ManoloMancelli/Persephone-Pro-Controller/Docs/V1/IMG/Arduino Uno Mini.png

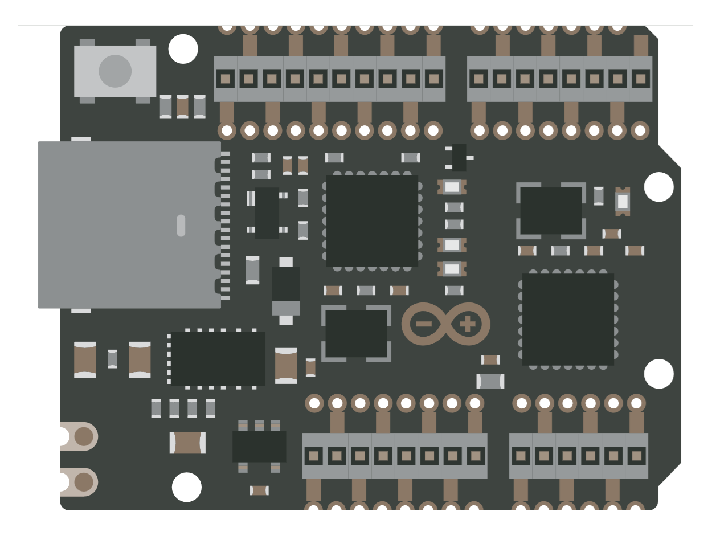
Docs/V1/IMG/Arduino Uno Mini.png
