ManoloMancelli/Persephone-Pro-Controller/img/V2/2.jpeg

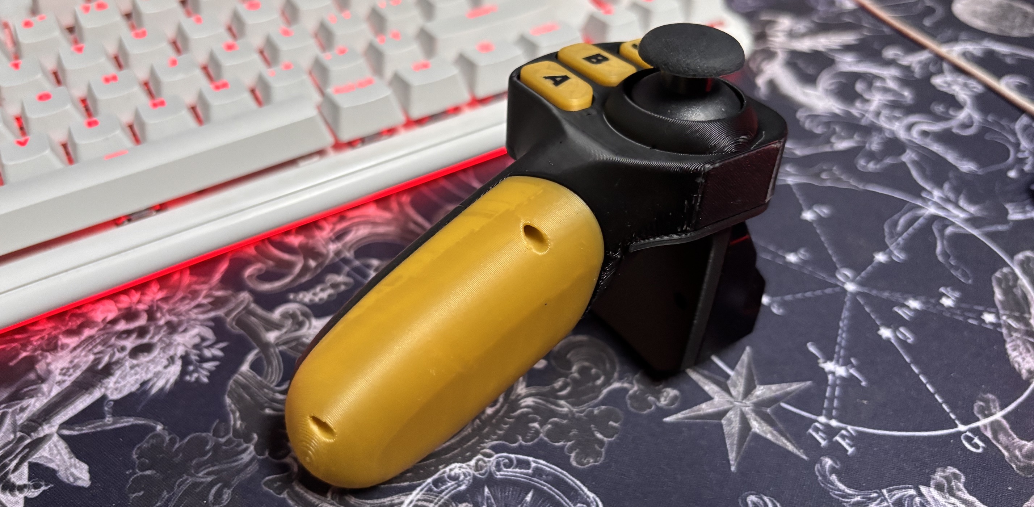
img/V2/2.jpeg
