ManoloMancelli/Persephone-Pro-Controller/img/V2/3.jpeg

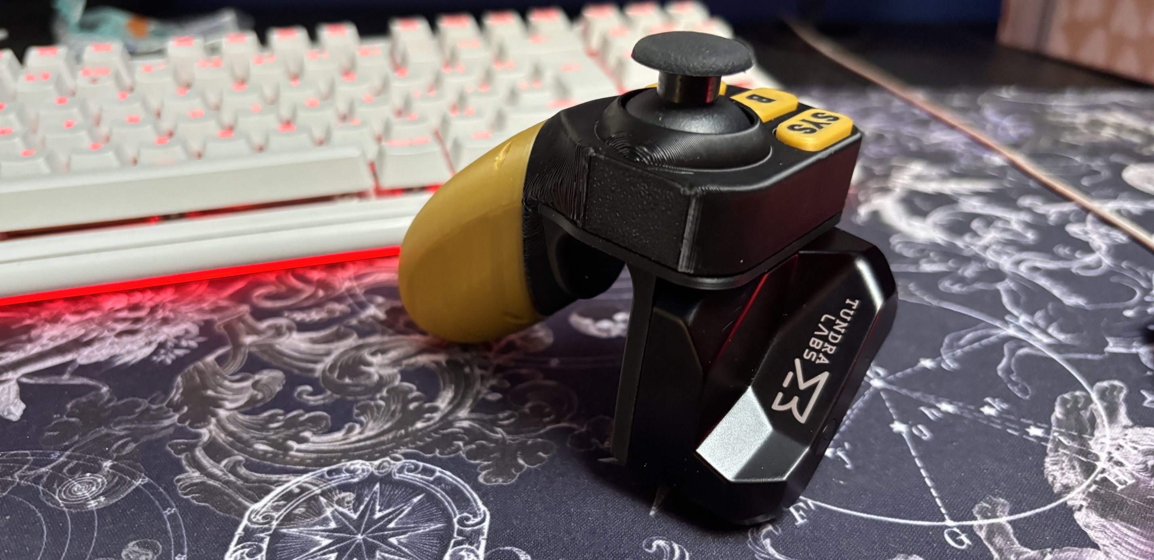
img/V2/3.jpeg
