ManoloMancelli/Persephone-Pro-Controller/Changelog/V1/img/11.01.2026/assembly3.jpeg

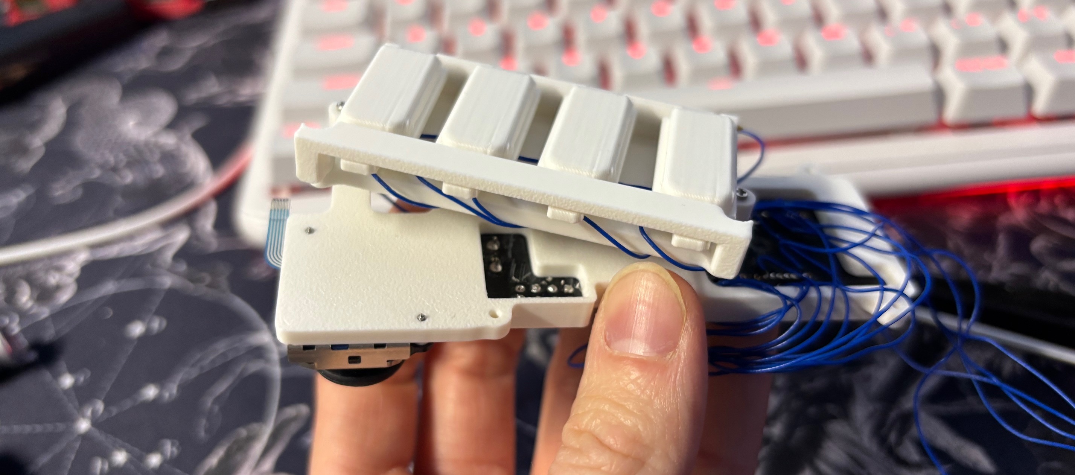
Changelog/V1/img/11.01.2026/assembly3.jpeg
