ManoloMancelli/Persephone-Pro-Controller/Changelog/V1/img/8.01.2026/array1.jpeg

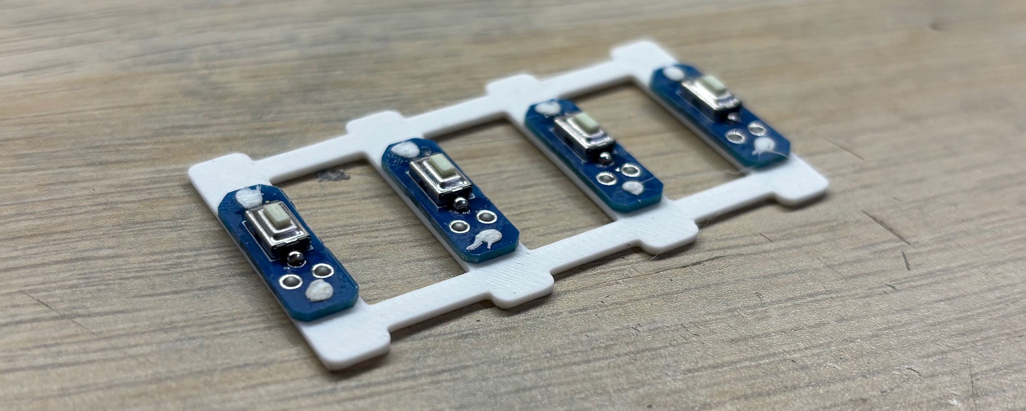
Changelog/V1/img/8.01.2026/array1.jpeg
