ManoloMancelli/Persephone-Pro-Controller/Changelog/V1/img/8.01.2026/joystick2.jpeg

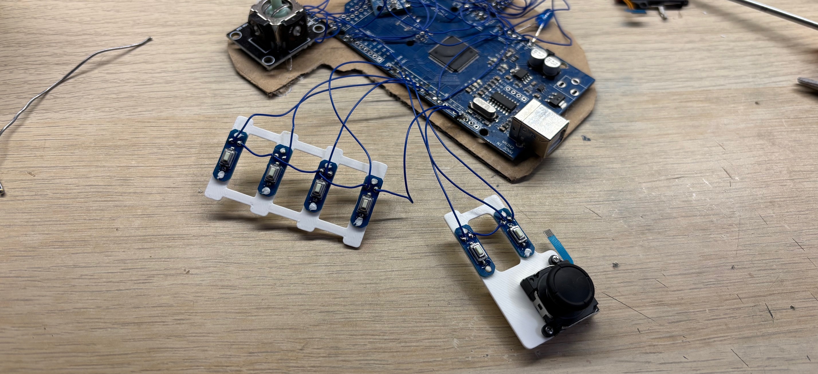
Changelog/V1/img/8.01.2026/joystick2.jpeg
