ManoloMancelli/Persephone-Pro-Controller/Changelog/V1/img/8.01.2026/prototype1.jpeg

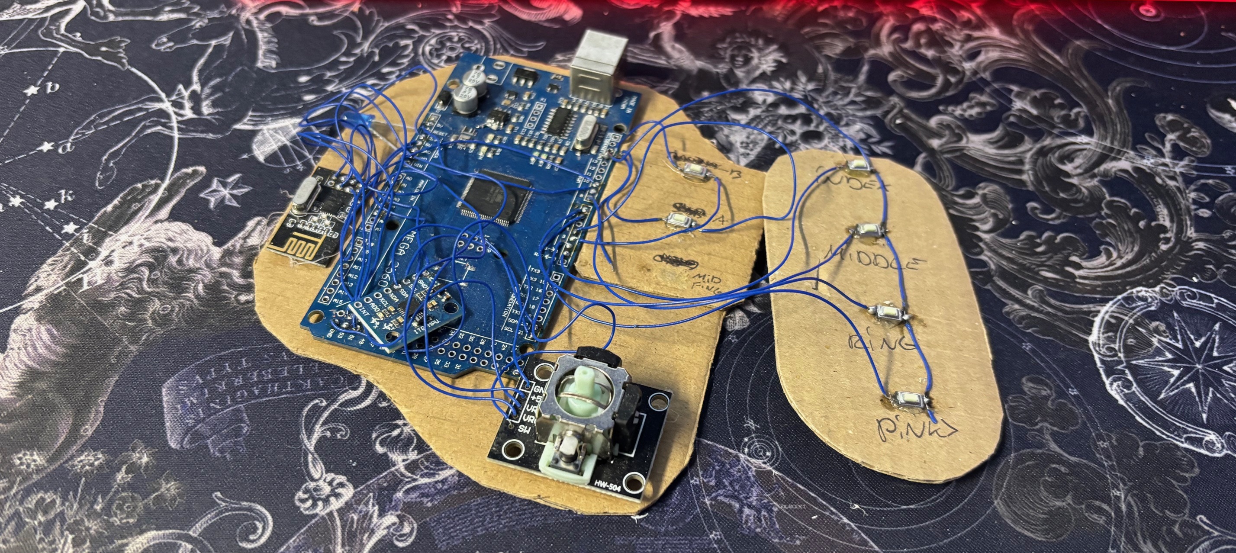
Changelog/V1/img/8.01.2026/prototype1.jpeg
