ManoloMancelli/Persephone-Pro-Controller/Changelog/V1/img/9.01.2026/connection1.jpeg

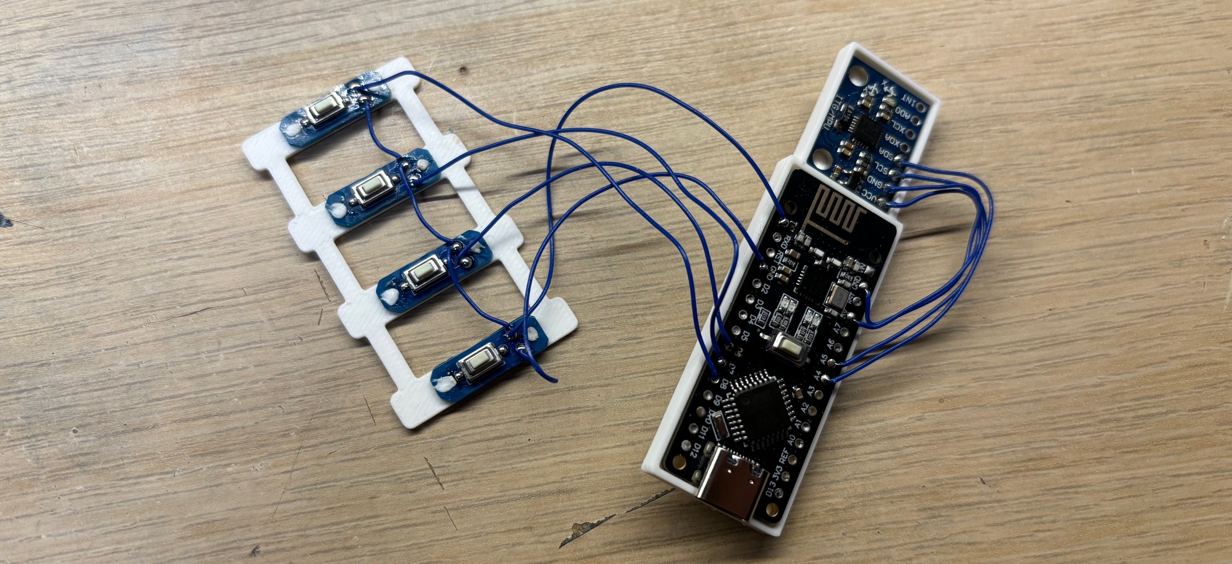
Changelog/V1/img/9.01.2026/connection1.jpeg
