ManoloMancelli/Persephone-Pro-Controller/Changelog/V1/img/9.01.2026/connection2.jpeg

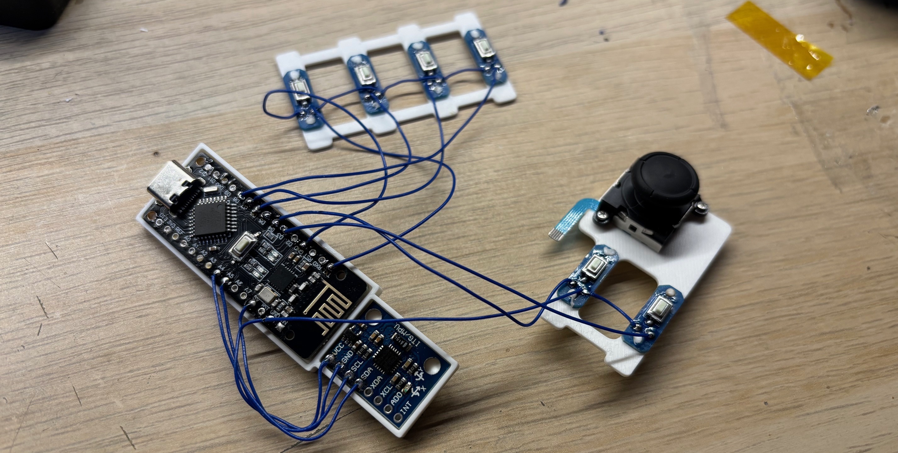
Changelog/V1/img/9.01.2026/connection2.jpeg
