ManoloMancelli/Persephone-Pro-Controller/Changelog/V1/img/10.01.2026/arduino1.png

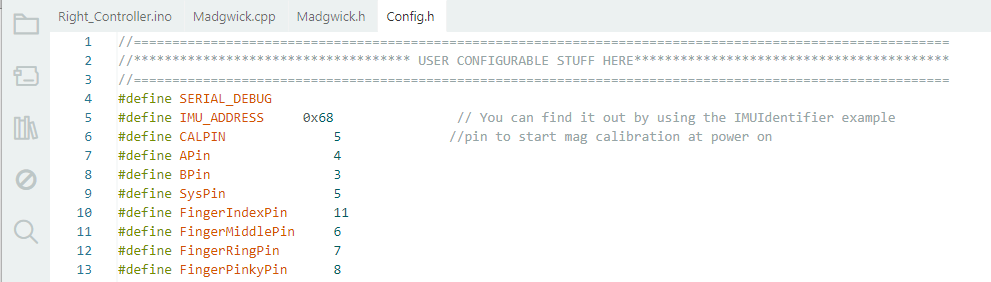
Changelog/V1/img/10.01.2026/arduino1.png
