ManoloMancelli/Persephone-Pro-Controller/Changelog/V1/img/10.01.2026/bracket2.jpeg

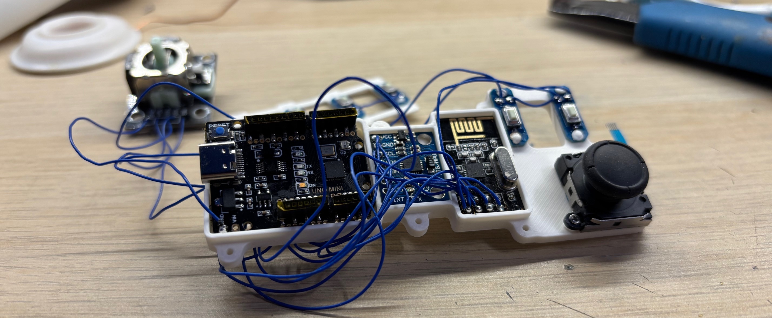
Changelog/V1/img/10.01.2026/bracket2.jpeg
