ManoloMancelli/Persephone-Pro-Controller/Changelog/V1/img/17.01.2026/joycon1.jpeg

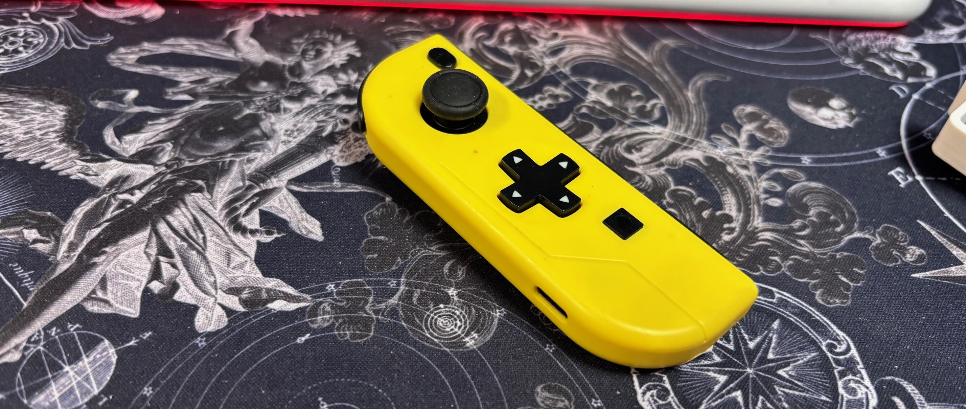
Changelog/V1/img/17.01.2026/joycon1.jpeg
