ManoloMancelli/Persephone-Pro-Controller/Changelog/V1/img/17.01.2026/joycon2.jpeg

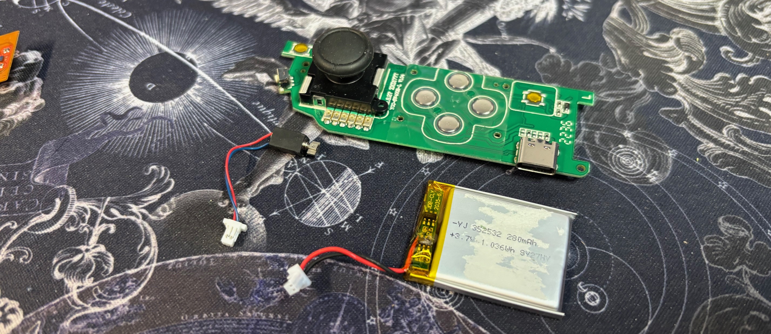
Changelog/V1/img/17.01.2026/joycon2.jpeg
