ManoloMancelli/Persephone-Pro-Controller/Changelog/V1/img/18.01.2026/bumper1.jpeg

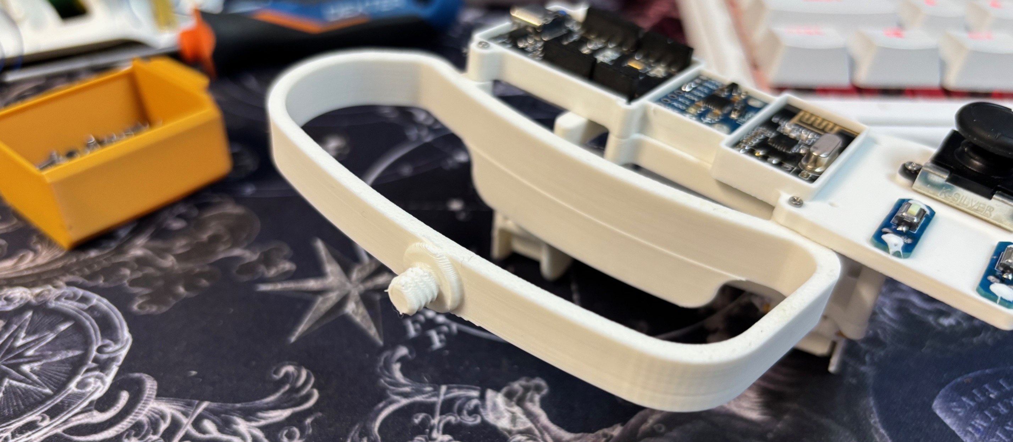
Changelog/V1/img/18.01.2026/bumper1.jpeg
