ManoloMancelli/Persephone-Pro-Controller/Changelog/V1/img/18.01.2026/palmrest.jpeg

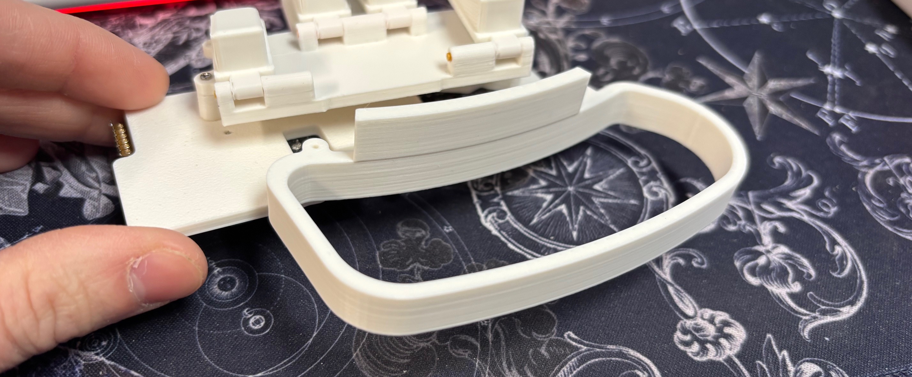
Changelog/V1/img/18.01.2026/palmrest.jpeg
